falo2k/ProtonPack/Images/bargraphwiring.jpg

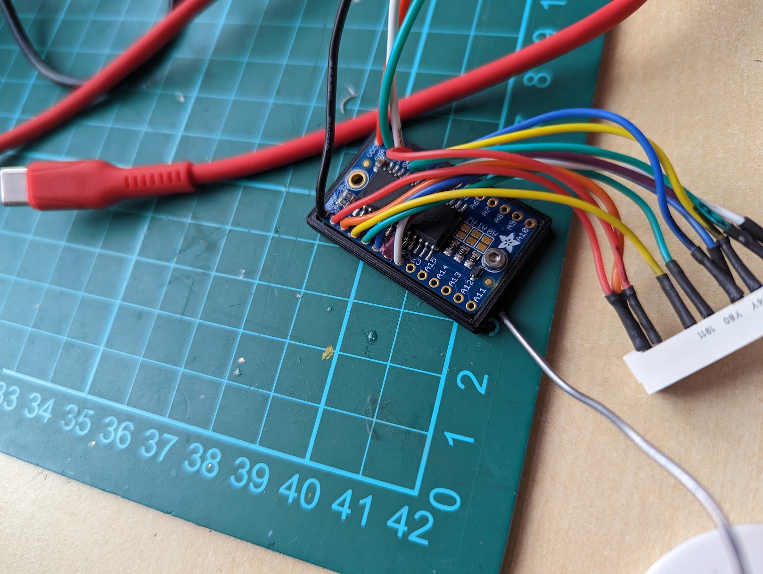
Images/bargraphwiring.jpg
